boaks/mobilebeehivescale/pictures/BausteineT91X.png

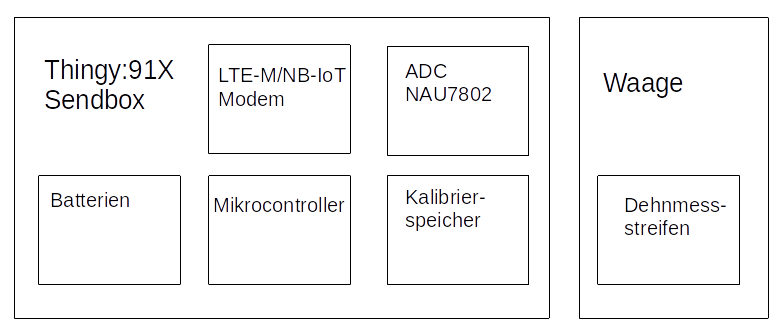
pictures/BausteineT91X.png
